SuperHouse/Z2T/Images/2019-11-23 11.11.57.jpg

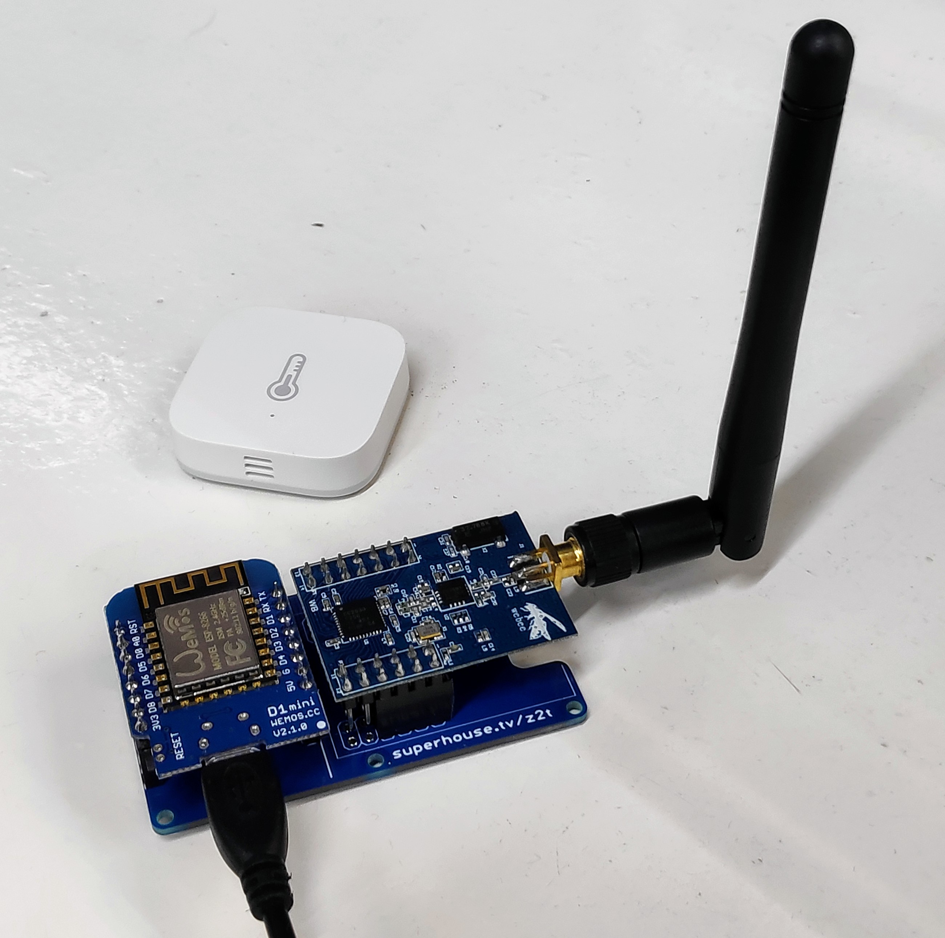
Images/2019-11-23 11.11.57.jpg
